juanCoder64/quantum/Ejemplos/brujula/brujula.ino

const unsigned char chabots [] PROGMEM = {
  //logo de chabots quantum en BMP para mostrarlo en la OLED
  0x00, 0x00, 0x00, 0x00, 0x00, 0x00, 0x00, 0x00, 0x00, 0x00, 0x00, 0x00, 0x00, 0x00, 0x00, 0x00,
  0x00, 0x00, 0x00, 0x00, 0x00, 0x00, 0x00, 0x00, 0x00, 0x00, 0x00, 0x00, 0x00, 0x00, 0x00, 0x00,
  0x00, 0x00, 0x00, 0x00, 0x00, 0x00, 0x00, 0x00, 0x00, 0x00, 0x00, 0x00, 0x00, 0x00, 0x00, 0x00,
  0x00, 0x00, 0x00, 0x00, 0x00, 0x00, 0x00, 0x00, 0x00, 0x00, 0x00, 0x00, 0x00, 0x00, 0x00, 0x00,
  0x00, 0x00, 0x00, 0x00, 0x00, 0x00, 0x00, 0x00, 0x00, 0x00, 0x00, 0x00, 0x00, 0x00, 0x00, 0x00,
  0x00, 0x00, 0x00, 0x00, 0x00, 0x00, 0x00, 0x00, 0x00, 0x00, 0x00, 0x00, 0x00, 0x00, 0x00, 0x00,
  0x00, 0x00, 0x00, 0x00, 0x00, 0x00, 0x00, 0x03, 0xff, 0xc0, 0x00, 0x00, 0x00, 0x00, 0x00, 0x00,
  0x00, 0x00, 0x00, 0x00, 0x00, 0x00, 0x00, 0x0f, 0xff, 0xf0, 0x00, 0x00, 0x00, 0x00, 0x00, 0x00,
  0x00, 0x00, 0x00, 0x00, 0x00, 0x00, 0x00, 0x3f, 0x00, 0x7c, 0x00, 0x00, 0x00, 0x00, 0x00, 0x00,
  0x00, 0x00, 0x00, 0x00, 0x00, 0x00, 0x00, 0xf8, 0x00, 0x0f, 0x00, 0x00, 0x00, 0x00, 0x00, 0x00,
  0x00, 0x00, 0x00, 0x00, 0x00, 0x00, 0x01, 0xe0, 0x00, 0x07, 0x80, 0x00, 0x00, 0x00, 0x00, 0x00,
  0x00, 0x00, 0x00, 0x00, 0x00, 0x00, 0x03, 0x80, 0x00, 0x01, 0xc0, 0x00, 0x00, 0x00, 0x00, 0x00,
  0x00, 0x00, 0x00, 0x00, 0x7f, 0xff, 0x07, 0x00, 0x00, 0x00, 0xe0, 0xff, 0xfe, 0x00, 0x00, 0x00,
  0x00, 0x00, 0x00, 0x03, 0xff, 0xff, 0xfe, 0x00, 0x00, 0x00, 0x7f, 0xff, 0xff, 0xc0, 0x00, 0x00,
  0x00, 0x00, 0x00, 0x07, 0xe0, 0x00, 0x1f, 0xc0, 0x00, 0x03, 0xf8, 0x00, 0x07, 0xe0, 0x00, 0x00,
  0x00, 0x00, 0x00, 0x0f, 0x80, 0x00, 0x18, 0x78, 0x00, 0x1e, 0x1c, 0x00, 0x01, 0xf0, 0x00, 0x00,
  0x00, 0x00, 0x00, 0x1f, 0x00, 0x00, 0x30, 0x07, 0x80, 0xe0, 0x0c, 0x00, 0x00, 0xf8, 0x00, 0x00,
  0x00, 0x00, 0x00, 0x1e, 0x00, 0x00, 0x60, 0x00, 0xf7, 0x00, 0x06, 0x00, 0x00, 0x78, 0x00, 0x00,
  0x00, 0x00, 0x00, 0x1e, 0x00, 0x00, 0x60, 0x00, 0x3c, 0x00, 0x06, 0x00, 0x00, 0x78, 0x00, 0x00,
  0x00, 0x00, 0x00, 0x1c, 0x00, 0x00, 0xc0, 0x01, 0xc3, 0x80, 0x03, 0x00, 0x00, 0x38, 0x00, 0x00,
  0x00, 0x00, 0x00, 0x0e, 0x00, 0x00, 0xc0, 0x06, 0x00, 0x60, 0x01, 0x00, 0x00, 0x78, 0x00, 0x00,
  0x00, 0x00, 0x00, 0x0e, 0x00, 0x01, 0x80, 0x18, 0x00, 0x0c, 0x01, 0x80, 0x00, 0x70, 0x00, 0x00,
  0x00, 0x00, 0x7f, 0xff, 0xff, 0xff, 0xff, 0xc0, 0x00, 0x03, 0xff, 0xff, 0xff, 0xff, 0xf8, 0x00,
  0x00, 0x00, 0x60, 0x00, 0x00, 0x00, 0x00, 0x00, 0x00, 0x00, 0x00, 0x00, 0x00, 0x00, 0x18, 0x00,
  0x00, 0x00, 0x60, 0x00, 0x00, 0x00, 0x00, 0x00, 0x00, 0x00, 0x00, 0x00, 0x00, 0x00, 0x18, 0x00,
  0x00, 0x00, 0x60, 0x00, 0x00, 0x00, 0x00, 0x00, 0x00, 0x00, 0x00, 0x00, 0x00, 0x00, 0x18, 0x00,
  0x00, 0x00, 0x60, 0x00, 0x00, 0x00, 0x00, 0x00, 0x00, 0x00, 0x00, 0x00, 0x00, 0x00, 0x18, 0x00,
  0x00, 0x00, 0x60, 0x00, 0x00, 0x00, 0x00, 0x00, 0x00, 0x00, 0x00, 0x00, 0x00, 0x00, 0x18, 0x00,
  0x00, 0x00, 0x00, 0x00, 0x00, 0x00, 0x00, 0x00, 0xff, 0x80, 0x00, 0x00, 0x00, 0x00, 0x00, 0x00,
  0x00, 0x00, 0x00, 0x00, 0x3e, 0x08, 0x10, 0x40, 0x80, 0x83, 0xe1, 0xfe, 0x7c, 0x00, 0x00, 0x00,
  0x00, 0x00, 0x00, 0x00, 0xc0, 0x08, 0x30, 0xe0, 0xff, 0x8c, 0x08, 0x20, 0x80, 0x00, 0x00, 0x00,
  0x00, 0x00, 0x00, 0x00, 0x80, 0x0f, 0xf1, 0x10, 0x80, 0x48, 0x0c, 0x20, 0x1e, 0x00, 0x00, 0x00,
  0x00, 0x00, 0x00, 0x00, 0x61, 0x88, 0x33, 0x18, 0xc0, 0x86, 0x18, 0x20, 0x86, 0x00, 0x00, 0x00,
  0x00, 0x00, 0x00, 0x00, 0x00, 0x00, 0x00, 0x00, 0x00, 0x00, 0x00, 0x00, 0x00, 0x00, 0x00, 0x00,
  0x00, 0x00, 0x00, 0x00, 0x00, 0x00, 0x00, 0x00, 0x00, 0x00, 0x00, 0x00, 0x00, 0x00, 0x00, 0x00,
  0x00, 0x00, 0x00, 0x00, 0x00, 0x00, 0x18, 0x00, 0x00, 0x00, 0x00, 0x00, 0x00, 0x00, 0x00, 0x00,
  0x00, 0x00, 0x00, 0x00, 0x00, 0x02, 0x0d, 0x20, 0x08, 0x92, 0x00, 0x00, 0x00, 0x00, 0x00, 0x00,
  0x00, 0x00, 0x00, 0x00, 0x00, 0x03, 0x09, 0x21, 0x24, 0x92, 0x49, 0x00, 0x00, 0x00, 0x08, 0x00,
  0x00, 0x00, 0x20, 0x00, 0x00, 0x01, 0x81, 0xa5, 0x24, 0x8a, 0x49, 0x00, 0x00, 0x00, 0x08, 0x00,
  0x00, 0x00, 0x20, 0x00, 0x00, 0x00, 0x18, 0x00, 0x00, 0x00, 0x00, 0x00, 0x00, 0x00, 0x08, 0x00,
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
};






#include <Movimiento.h>
#include <Wire.h>
#include <Adafruit_Sensor.h>
#include <Adafruit_BNO055.h>
#include <Adafruit_GFX.h>
#include <Adafruit_SSD1306.h>
Adafruit_SSD1306 disp(128, 64, &Wire, 4);
float vuelta = 180;
float ini;
int l1;
Movimiento mueve(1, 2, 3);
int adelante;
float headingDegrees;
float led;
float valor;
Adafruit_BNO055 osas = Adafruit_BNO055(55, 0x28);
void brujula() {
  sensors_event_t orientationData , linearAccelData;
  osas.getEvent(&orientationData, Adafruit_BNO055::VECTOR_EULER);
  valor = orientationData.orientation.x;
}
void setup() {
  Serial.begin(9600);
  Wire.begin();
  osas.begin();
  disp.begin(SSD1306_SWITCHCAPVCC, 0x3C);
  disp.clearDisplay();
  disp.drawBitmap(0, 0, chabots, 128, 64, WHITE);
  disp.display();
  delay(2000);//se espera mientras se imprime el logo de chabots quantum
}

void loop() {
  disp.clearDisplay();
  brujula();
  disp.setTextSize(2);
  disp.setTextColor(WHITE);
  disp.setCursor(0, 0);
  disp.println("orientado");
  if (frente() == 0) {
    disp.clearDisplay();
    disp.setTextSize(2);
    disp.setTextColor(WHITE);
    disp.setCursor(0, 0);
    disp.println("orientando");
    mueve.rota(valor);//se orienta con control Proporcional
  }
  else {
    mueve.recio(); 
  }
  int temp = osas.getTemp();
  disp.setTextSize(1);
  disp.setCursor(0, 25);
  disp.println("pwm");
  disp.setCursor(0, 35);
  disp.println();
  disp.setCursor(50, 25);
  disp.println("grados");
  disp.setCursor(50, 35);
  disp.println(valor);
  disp.println("temperatura");
  disp.setCursor(0, 55);
  disp.println(temp);
  disp.display();
  analogWrite(13, led);
  Serial.println(valor);
}
int frente() {
  if (valor < 10 || valor > 350) {
    return 1;
  }
  else {
    return 0;
  }
}
